Geolodthedwarf/PlanBook/planbook-cables/planbook-charger-cable.png

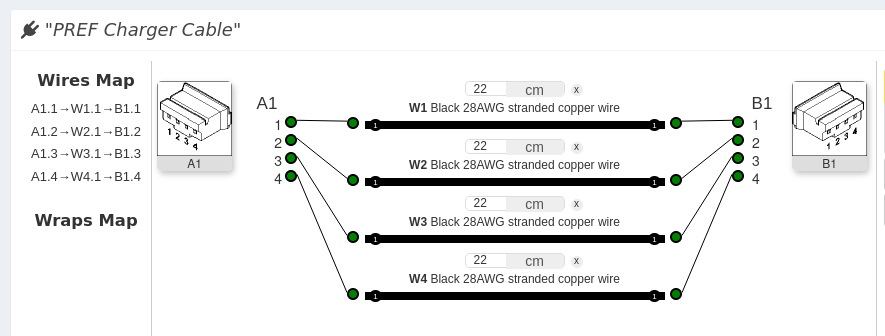
planbook-cables/planbook-charger-cable.png
