Geolodthedwarf/PlanBook/planbook-wifi/3d-models/User Library-PCIe_M_2_Key-E_2230_RF.STEP

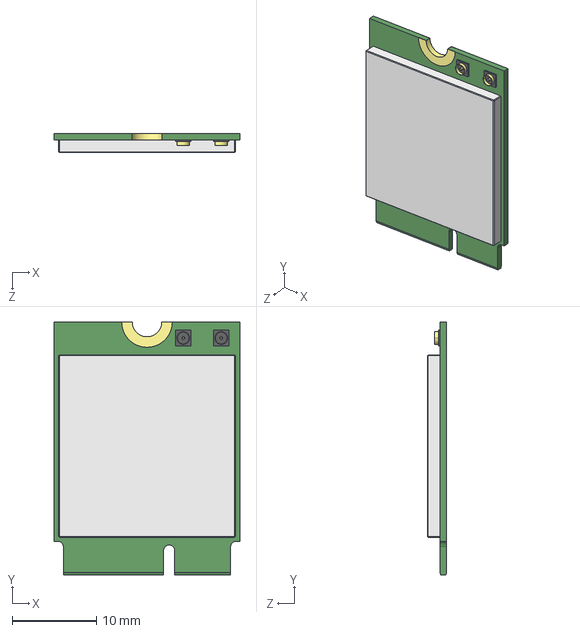
[picture p18: CAD file, 2026-09-27]
planbook-wifi/3d-models/User Library-PCIe_M_2_Key-E_2230_RF.STEP
22.0 x 30.0 x 2.30 mm
