Geolodthedwarf/PlanBook/planbook-3d-printed-parts/battery-holder-2025-11-18/PlanBook_Batt_Holder_18_11_25_V3_Mirrored.stl

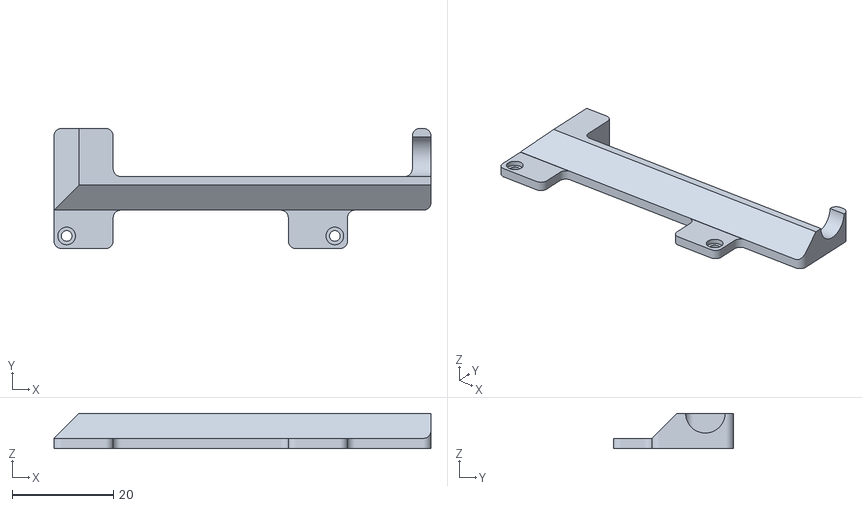
[picture p19: CAD file, 2026-09-27]
planbook-3d-printed-parts/battery-holder-2025-11-18/PlanBook_Batt_Holder_18_11_25_V3_Mirrored.stl
74.5 x 23.8 x 7.00
