Geolodthedwarf/PlanBook/planbook-case-20231121/PLANBOOK-bottom_enclosure_2023.09.06.step

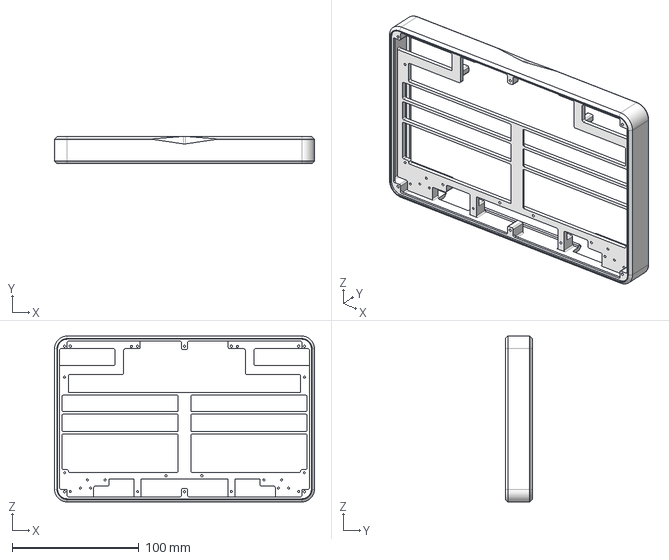
[picture p20: CAD file, 2026-09-27]
planbook-case-20231121/PLANBOOK-bottom_enclosure_2023.09.06.step
205.4 x 21.7 x 131.0 mm
