Geolodthedwarf/PlanBook/planbook-charger/3d-models/S2B-PH-SM4-TB.stp

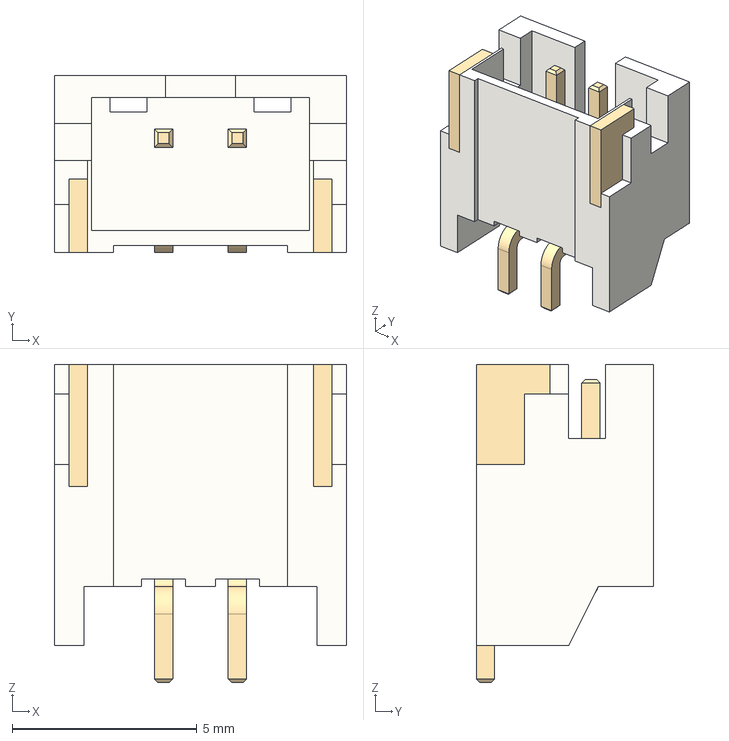
[picture p21: CAD file, 2026-09-27]
planbook-charger/3d-models/S2B-PH-SM4-TB.stp
7.90 x 4.80 x 8.60 mm
