Geolodthedwarf/PlanBook/planbook-headphones/3d-models/SR42W001.stp

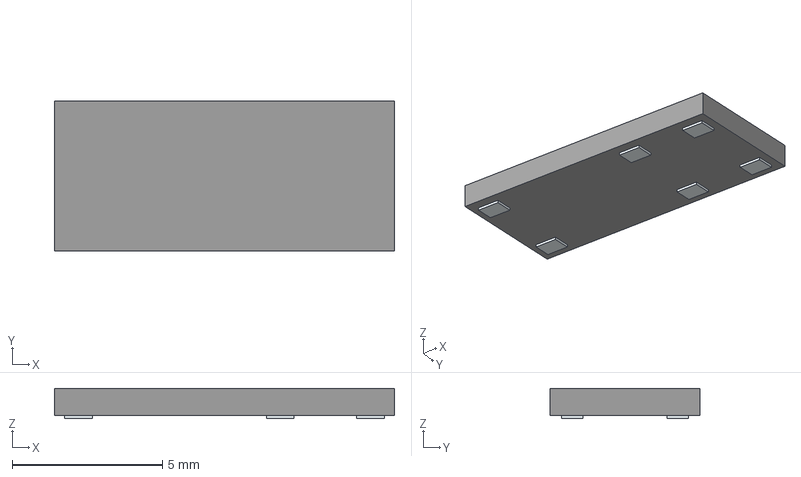
[picture p22: CAD file, 2026-09-27]
planbook-headphones/3d-models/SR42W001.stp
11.3 x 5.00 x 1.00 mm
Pins
