Geolodthedwarf/PlanBook/planbook-keyboard-kailh-ortho/3d-models/S4B-PH-SM4-TB.stp

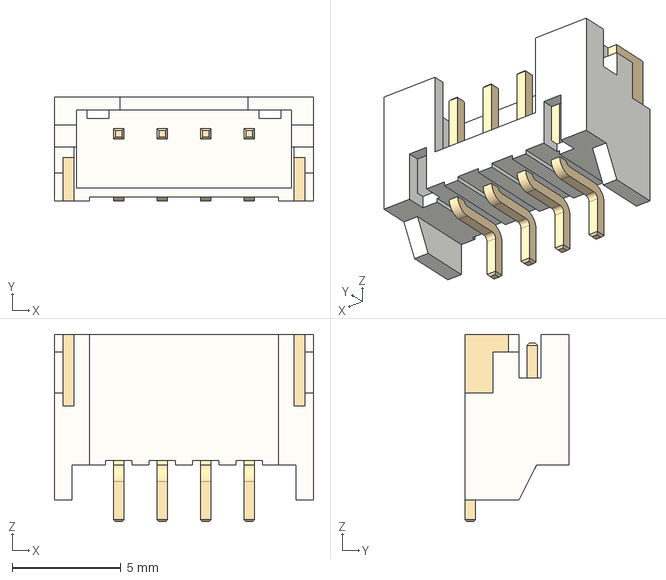
[picture p23: CAD file, 2026-09-27]
planbook-keyboard-kailh-ortho/3d-models/S4B-PH-SM4-TB.stp
11.9 x 4.80 x 8.60 mm
