Geolodthedwarf/PlanBook/planbook-wifi/3d-models/SM02B-SRSS-TB-LF--SN---3DModel-STEP-56544.STEP

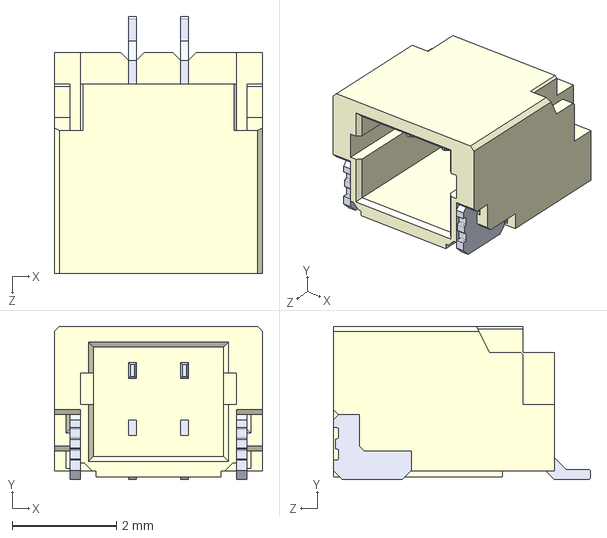
[picture p24: CAD file, 2026-09-27]
planbook-wifi/3d-models/SM02B-SRSS-TB-LF--SN---3DModel-STEP-56544.STEP
4.00 x 2.95 x 4.95 mm
