Geolodthedwarf/PlanBook/planbook-charger/3d-models/User Library-MWSA0518S.STEP

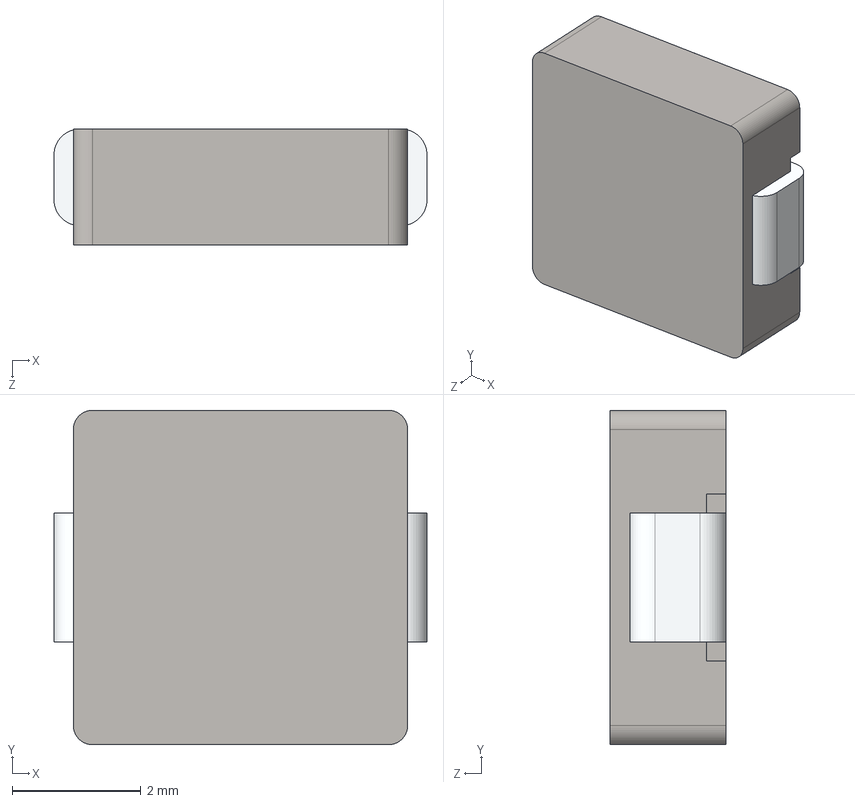
[picture p25: CAD file, 2026-09-27]
planbook-charger/3d-models/User Library-MWSA0518S.STEP
5.80 x 5.20 x 1.80 mm
MWSA0518S-HOUSE
MWSA0518S-PIN
