Geolodthedwarf/PlanBook/planbook-keyboard-kailh-ortho/3d-models/W25Q32JVSSIQ--3DModel-STEP-269445.STEP

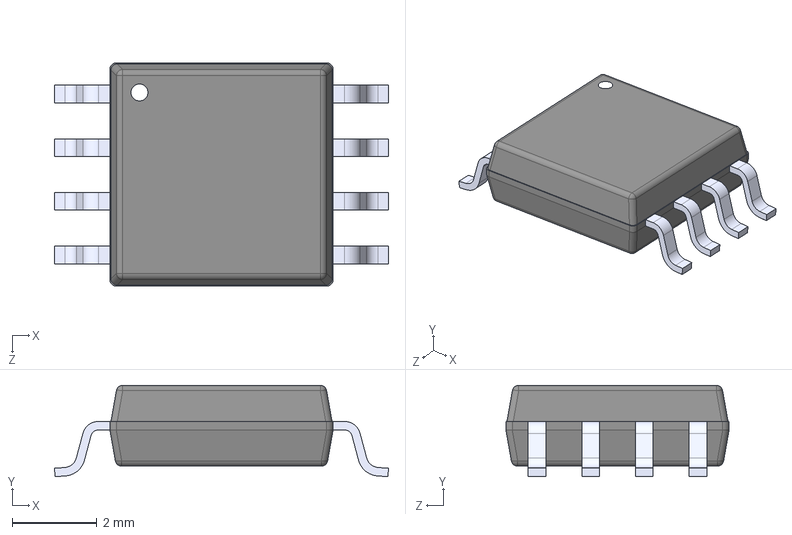
[picture p26: CAD file, 2026-09-27]
planbook-keyboard-kailh-ortho/3d-models/W25Q32JVSSIQ--3DModel-STEP-269445.STEP
7.90 x 2.16 x 5.28 mm
