Geolodthedwarf/PlanBook/planbook-motherboard/3d-models/SOD-128.step

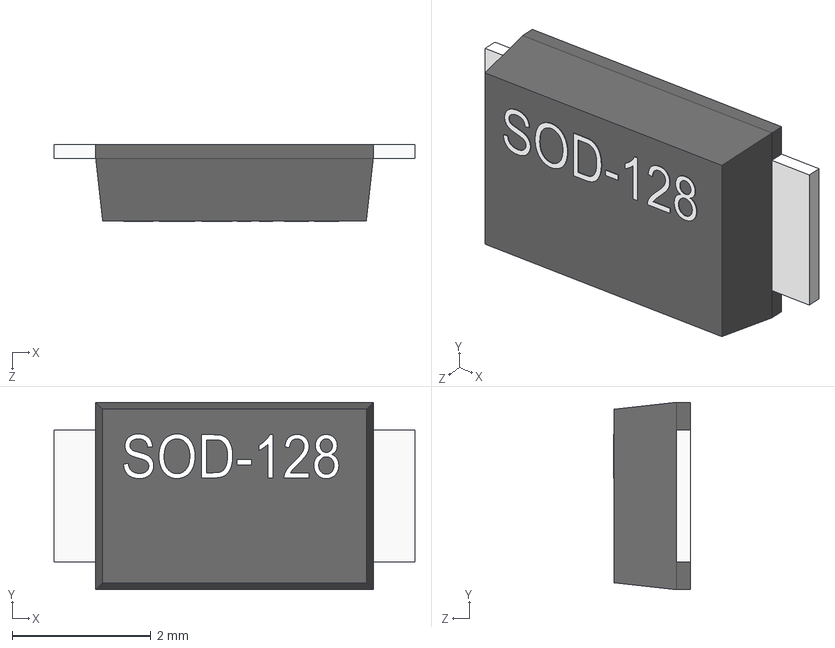
[picture p27: CAD file, 2026-09-27]
planbook-motherboard/3d-models/SOD-128.step
5.20 x 2.70 x 1.11 mm
