Geolodthedwarf/PlanBook/planbook-wifi/3d-models/CUI_SJ-43516-SMT-TR.step

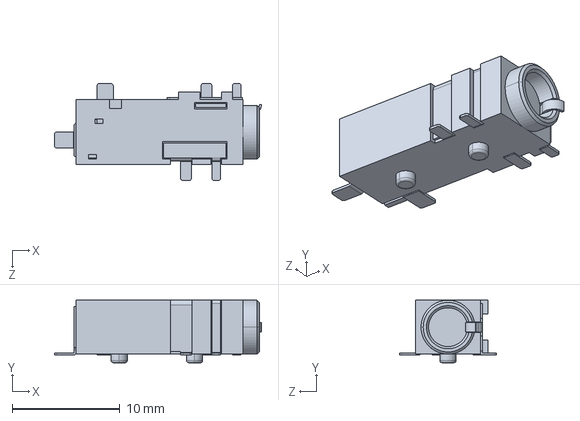
[picture p28: CAD file, 2026-09-27]
planbook-wifi/3d-models/CUI_SJ-43516-SMT-TR.step
19.2 x 5.80 x 9.00 mm
