Geolodthedwarf/PlanBook/planbook-charger/3d-models/S9B-PH-SM4-TB.stp

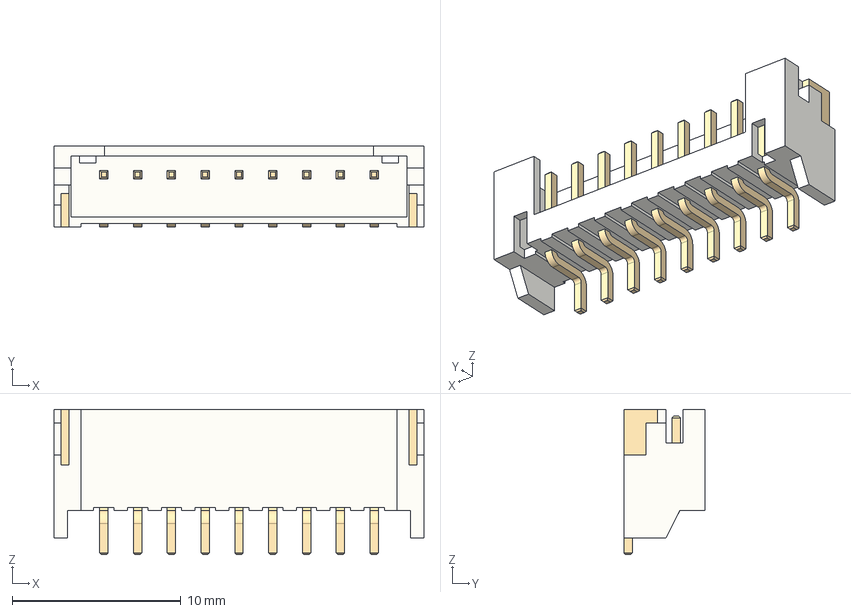
[picture p29: CAD file, 2026-09-27]
planbook-charger/3d-models/S9B-PH-SM4-TB.stp
21.9 x 4.80 x 8.60 mm
