Geolodthedwarf/PlanBook/planbook-headphones/3d-models/SM05B-SRSS-TB(LF)(SN)--3DModel-STEP-418109.STEP

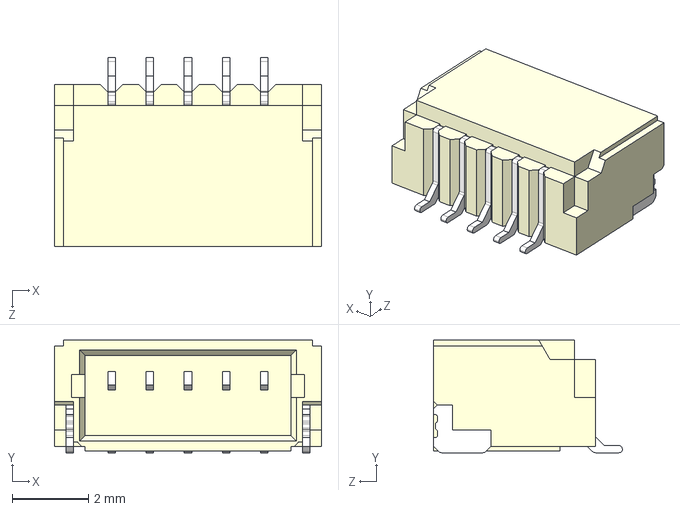
[picture p30: CAD file, 2026-09-27]
planbook-headphones/3d-models/SM05B-SRSS-TB(LF)(SN)--3DModel-STEP-418109.STEP
7.00 x 2.95 x 4.95 mm
