Geolodthedwarf/PlanBook/planbook-keyboard-kailh-ortho/3d-models/KMR221GLFS.step

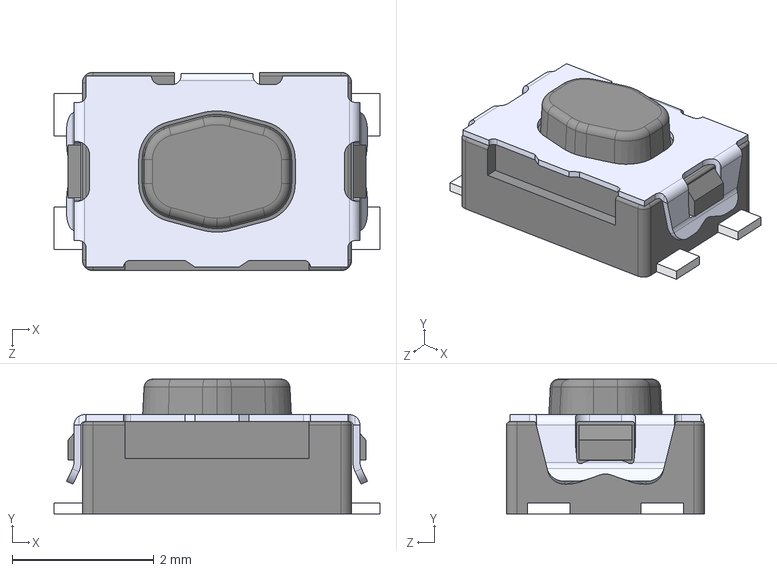
[picture p31: CAD file, 2026-09-27]
planbook-keyboard-kailh-ortho/3d-models/KMR221GLFS.step
4.60 x 1.90 x 2.80 mm
