Geolodthedwarf/PlanBook/planbook-motherboard/3d-models/SON95P300X300X80-7N.step

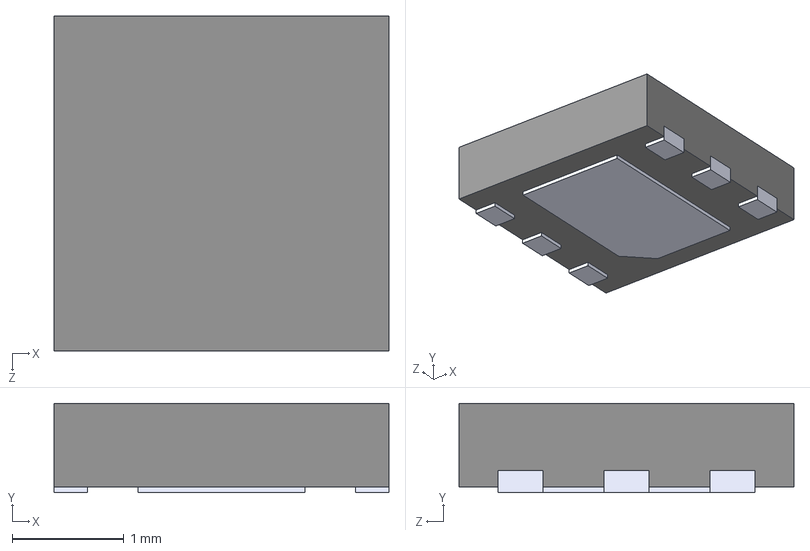
[picture p32: CAD file, 2026-09-27]
planbook-motherboard/3d-models/SON95P300X300X80-7N.step
3.00 x 0.8 x 3.00 mm
