Geolodthedwarf/PlanBook/planbook-motherboard/3d-models/CM2020-00TR--3DModel-STEP-56544.STEP

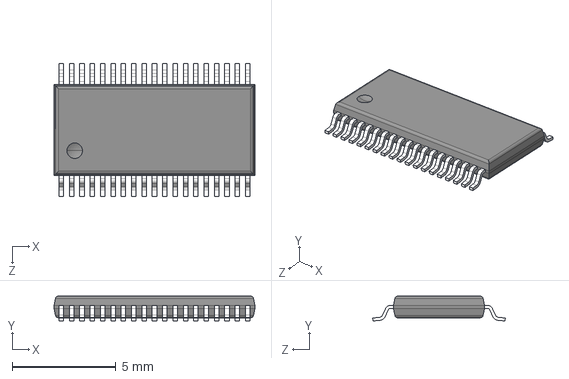
[picture p33: CAD file, 2026-09-27]
planbook-motherboard/3d-models/CM2020-00TR--3DModel-STEP-56544.STEP
9.70 x 1.20 x 6.40 mm
