Geolodthedwarf/PlanBook/planbook-motherboard/3d-models/User Library-VQFN-100 12X12 40P.STEP

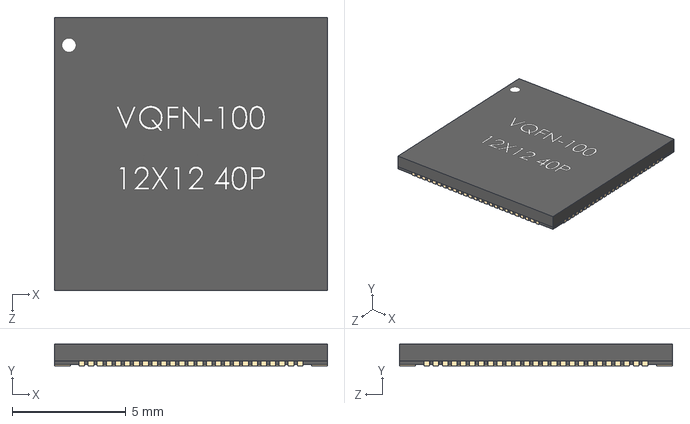
[picture p34: CAD file, 2026-09-27]
planbook-motherboard/3d-models/User Library-VQFN-100 12X12 40P.STEP
12.0 x 0.951 x 12.0 mm
