Geolodthedwarf/PlanBook/planbook-motherboard/3d-models/IND_TAIYO_NRH3012_TAY.step

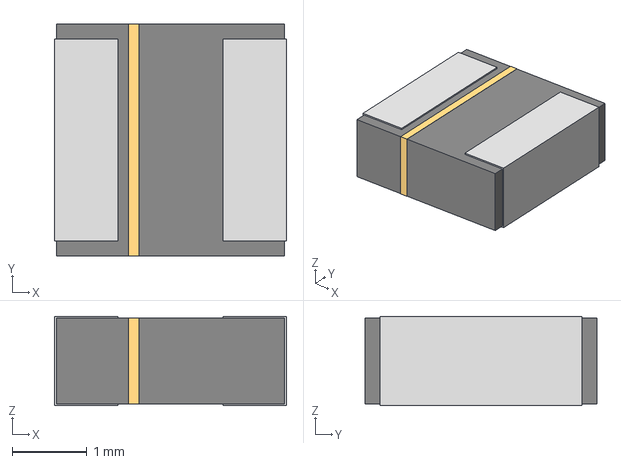
[picture p35: CAD file, 2026-09-27]
planbook-motherboard/3d-models/IND_TAIYO_NRH3012_TAY.step
3.10 x 3.10 x 1.19 mm
