Geolodthedwarf/PlanBook/planbook-wifi/3d-models/c-2199119-4-c-3d.stp

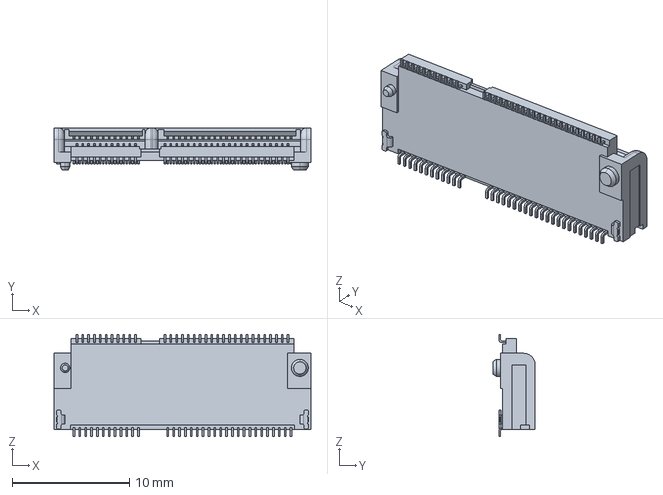
[picture p36: CAD file, 2026-09-27]
planbook-wifi/3d-models/c-2199119-4-c-3d.stp
21.9 x 3.62 x 8.70 mm
