Geolodthedwarf/PlanBook/planbook-motherboard/3d-models/HDMI-SMD_BX-HDMI-2-M19P.step

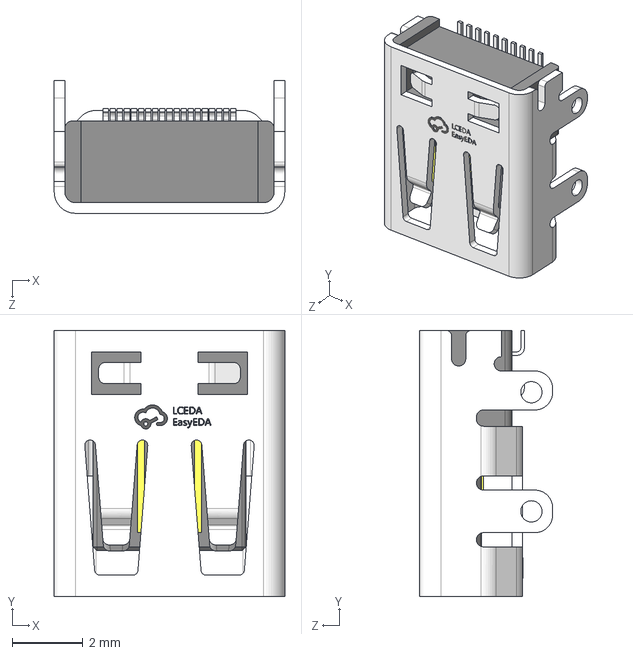
[picture p37: CAD file, 2026-09-27]
planbook-motherboard/3d-models/HDMI-SMD_BX-HDMI-2-M19P.step
6.50 x 7.50 x 3.76 mm
