Geolodthedwarf/PlanBook/planbook-motherboard/3d-models/DM3AT-SF-PEJM5--3DModel-STEP-56544.STEP

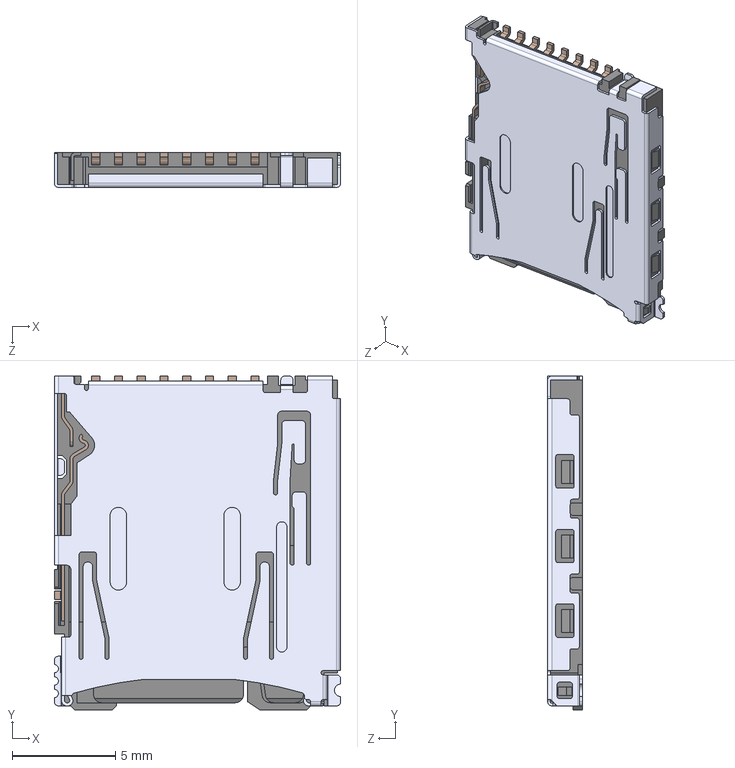
[picture p38: CAD file, 2026-09-27]
planbook-motherboard/3d-models/DM3AT-SF-PEJM5--3DModel-STEP-56544.STEP
13.8 x 16.2 x 1.68 mm
