Geolodthedwarf/PlanBook/planbook-motherboard/3d-models/c-1717254-1-d1-3d.stp

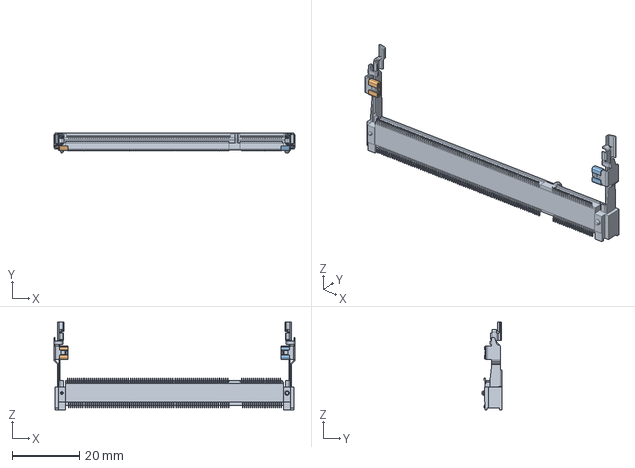
[picture p39: CAD file, 2026-09-27]
planbook-motherboard/3d-models/c-1717254-1-d1-3d.stp
71.5 x 5.90 x 26.0 mm
