Geolodthedwarf/PlanBook/planbook-motherboard/3d-models/ssfv33r_1stlf.stp

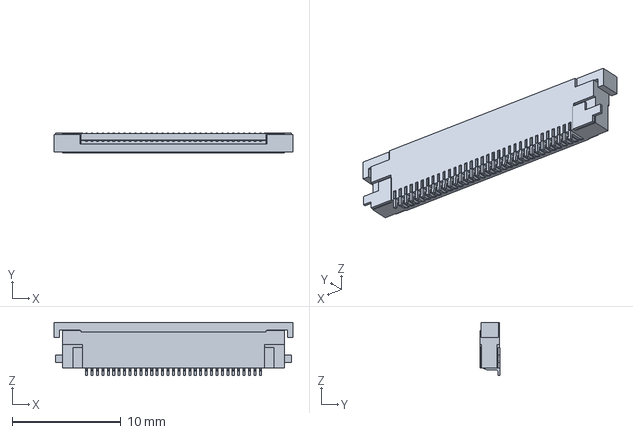
[picture p40: CAD file, 2026-09-27]
planbook-motherboard/3d-models/ssfv33r_1stlf.stp
22.0 x 1.87 x 4.90 mm
