Geolodthedwarf/PlanBook/planbook-motherboard/3d-models/BK-879.STEP

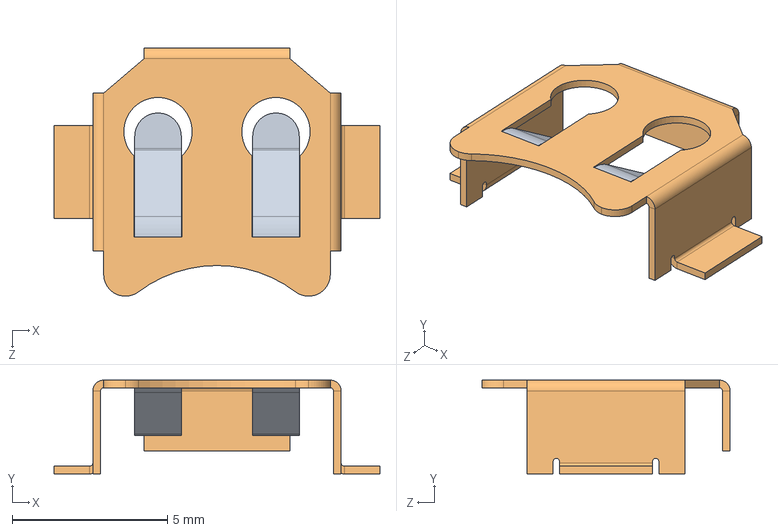
[picture p41: CAD file, 2026-09-27]
planbook-motherboard/3d-models/BK-879.STEP
10.5 x 3.02 x 8.00 mm
