Geolodthedwarf/PlanBook/planbook-motherboard/3d-models/FUSB302BMPX.STEP

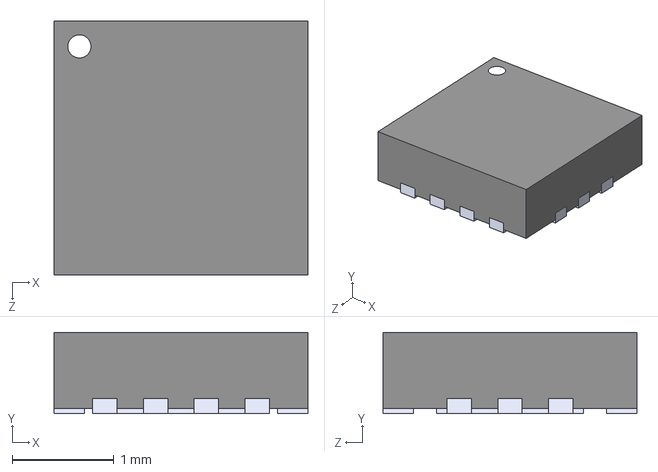
[picture p43: CAD file, 2026-09-27]
planbook-motherboard/3d-models/FUSB302BMPX.STEP
2.50 x 0.8 x 2.50 mm
