Geolodthedwarf/PlanBook/planbook-motherboard/3d-models/DM3CS-SF.stp

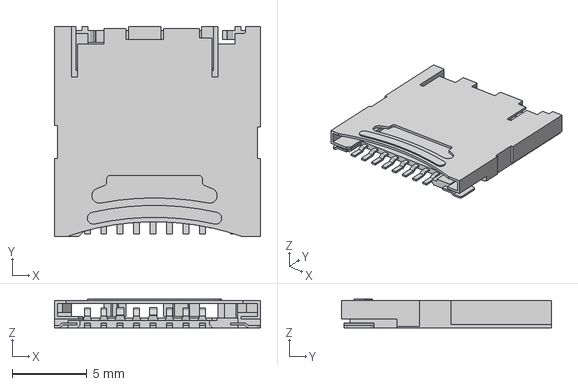
[picture p44: CAD file, 2026-09-27]
planbook-motherboard/3d-models/DM3CS-SF.stp
13.8 x 14.1 x 1.93 mm
