Geolodthedwarf/PlanBook/planbook-motherboard/3d-models/p36-2.stp

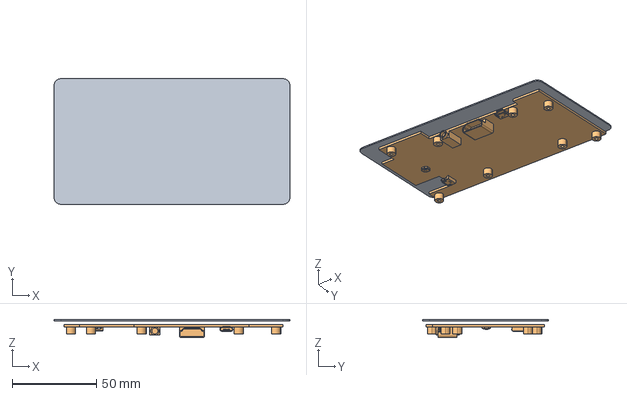
[picture p46: CAD file, 2026-09-27]
planbook-motherboard/3d-models/p36-2.stp
140.4 x 74.8 x 10.8 mm
