Geolodthedwarf/PlanBook/planbook-motherboard/3d-models/TSM-106-02-X-SH-A.step

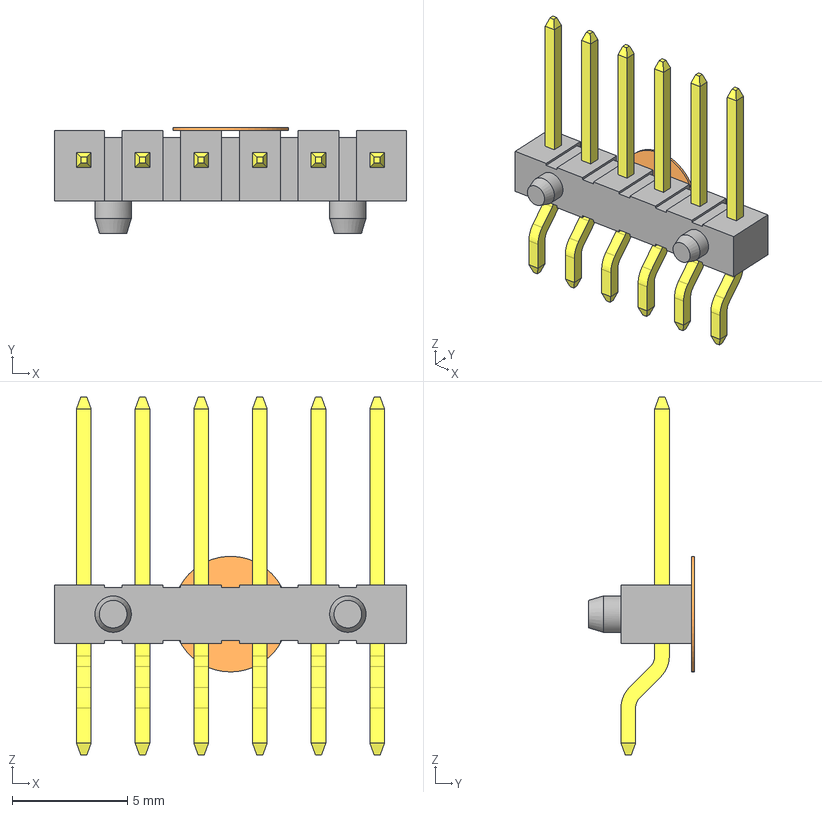
[picture p47: CAD file, 2026-09-27]
planbook-motherboard/3d-models/TSM-106-02-X-SH-A.step
15.2 x 4.57 x 15.5 mm
T-1S6-15(-02-6-SH)
TSM_polyimide_film
TSM-106-02-SH-A_body
