Geolodthedwarf/PlanBook/planbook-motherboard/3d-models/TLV320AIC3100IRHBR.STEP

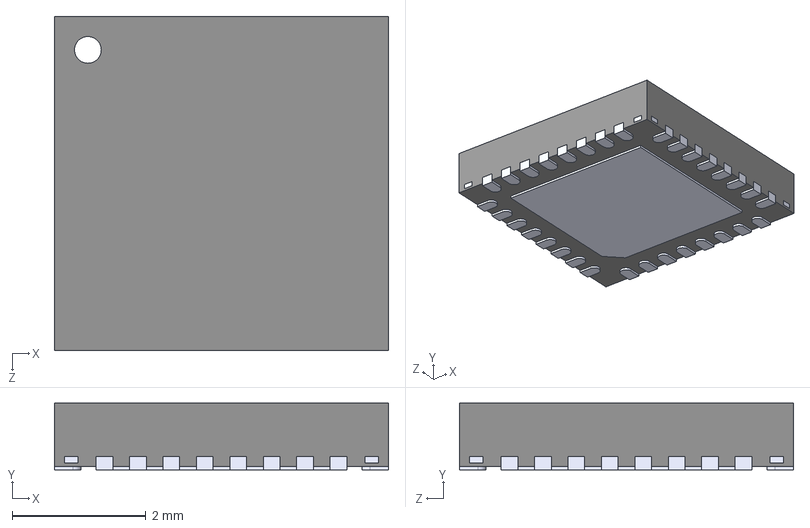
[picture p48: CAD file, 2026-09-27]
planbook-motherboard/3d-models/TLV320AIC3100IRHBR.STEP
5.00 x 1.00 x 5.00 mm
