Geolodthedwarf/PlanBook/planbook-motherboard/3d-models/IHLP4040DZ (2.2-100uH).STEP

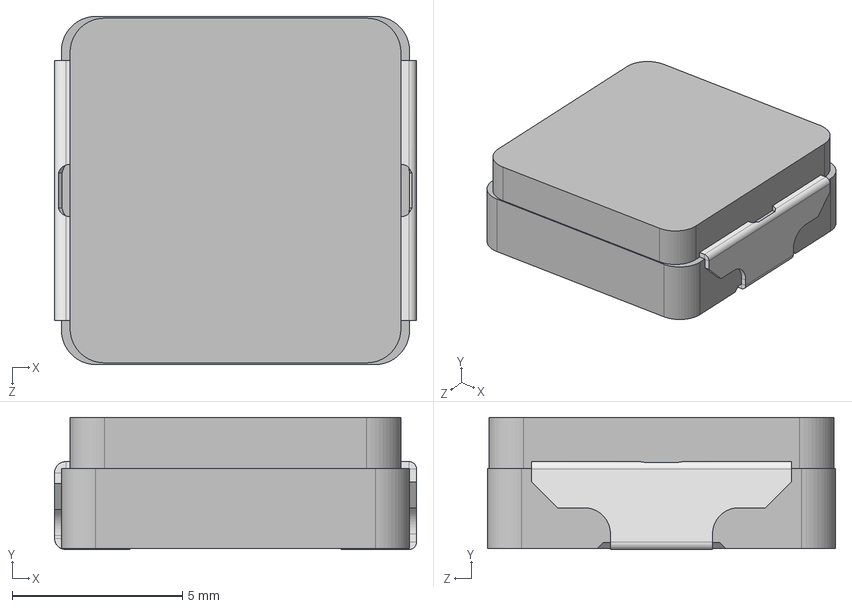
[picture p49: CAD file, 2026-09-27]
planbook-motherboard/3d-models/IHLP4040DZ (2.2-100uH).STEP
10.6 x 3.87 x 10.2 mm
