Geolodthedwarf/PlanBook/planbook-motherboard/3d-models/MP23ABS1TR.obj

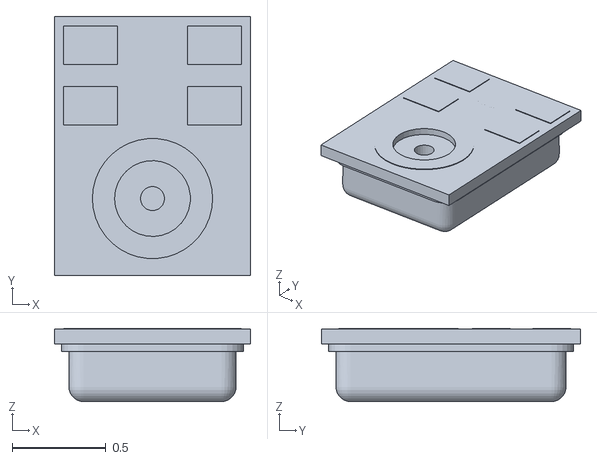
[picture p50: CAD file, 2026-09-27]
planbook-motherboard/3d-models/MP23ABS1TR.obj
1.04 x 1.38 x 0.39
