Geolodthedwarf/PlanBook/planbook-motherboard/3d-models/19-337-R6GHBHC-A01-2T.STEP

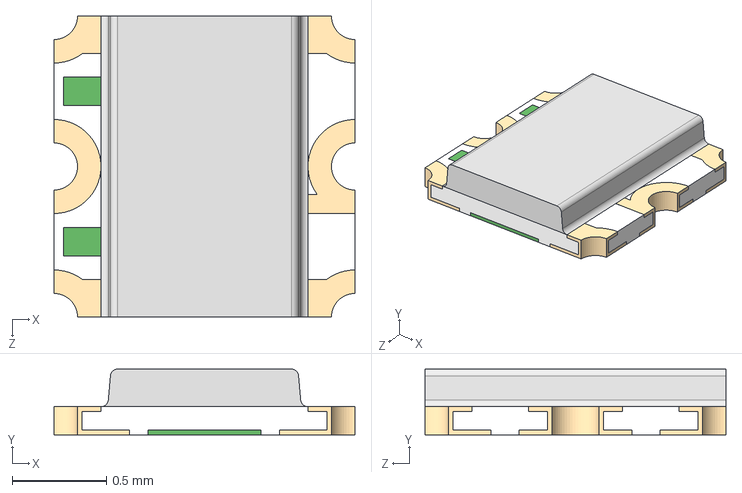
[picture p51: CAD file, 2026-09-27]
planbook-motherboard/3d-models/19-337-R6GHBHC-A01-2T.STEP
1.60 x 0.35 x 1.60 mm
