Geolodthedwarf/PlanBook/planbook-motherboard/3d-models/TYPE-C-31-M-12--3DModel-STEP-56544.STEP

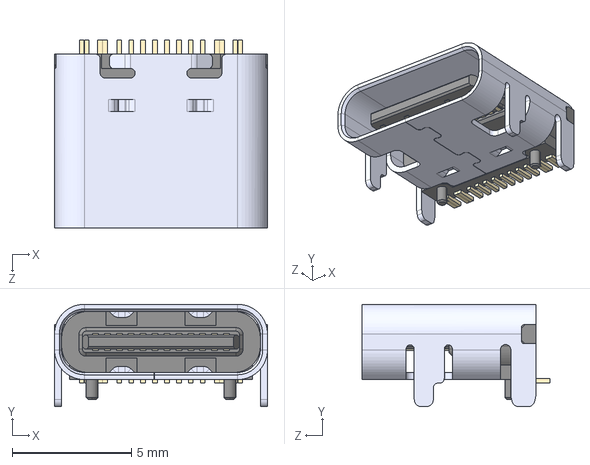
[picture p52: CAD file, 2026-09-27]
planbook-motherboard/3d-models/TYPE-C-31-M-12--3DModel-STEP-56544.STEP
8.94 x 4.30 x 7.90 mm
