Geolodthedwarf/PlanBook/planbook-motherboard/3d-models/Bateria 18650 3.7 V 1300 mAh d.18 mm.STEP

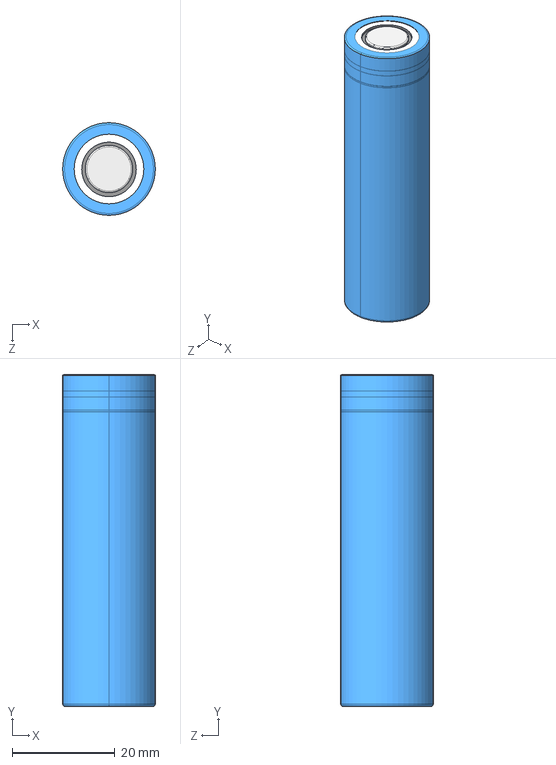
[picture p53: CAD file, 2026-09-27]
planbook-motherboard/3d-models/Bateria 18650 3.7 V 1300 mAh d.18 mm.STEP
18.1 x 64.7 x 18.1 mm
