Geolodthedwarf/PlanBook/planbook-motherboard/3d-models/keystone-PN54.STEP

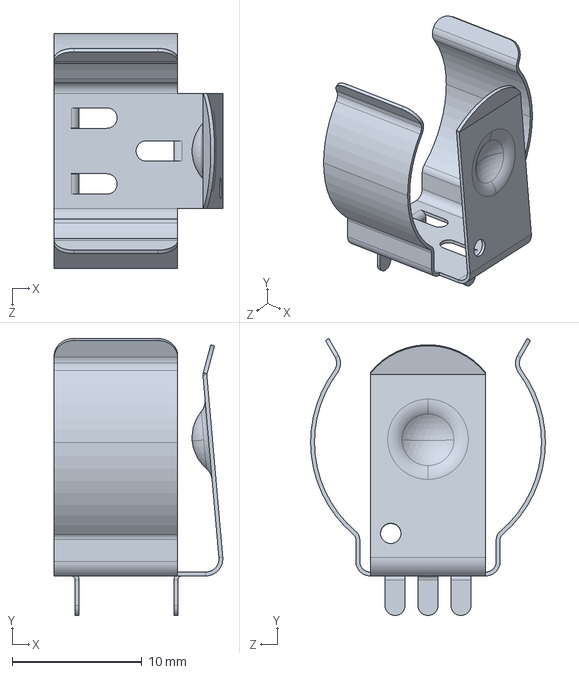
[picture p54: CAD file, 2026-09-27]
planbook-motherboard/3d-models/keystone-PN54.STEP
13.0 x 21.4 x 18.1 mm
