Geolodthedwarf/PlanBook/planbook-motherboard/3d-models/STP_NIT8M_SOM_REV10_20190228.step

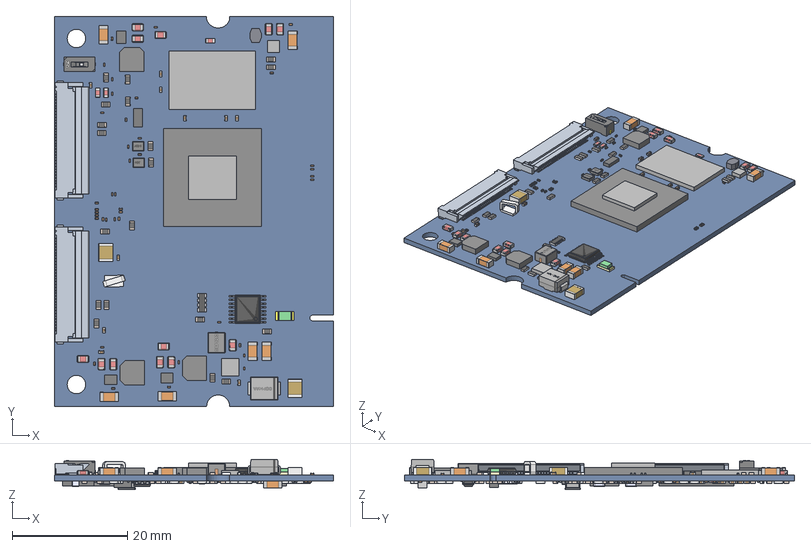
[picture p55: CAD file, 2026-09-27]
planbook-motherboard/3d-models/STP_NIT8M_SOM_REV10_20190228.step
48.4 x 67.6 x 5.23 mm
Board
CAP0201_(0603) x 175
cay16-j4 x 2
Extruded x 16
CAP0402 x 43
CAPC3225X13 x 2
Chip_Cap_MLCC_1206_(3216)_D x 7
SW3dPS-LED1206G_Extruded
SW3dPS-LED1206G_Extruded4
SW3dPS-LED1206G_Extruded2 x 2
SW3dPS-LED1206G_Extruded1
SW3dPS-LED1206G_Extruded3
SW3dPS-LED1206G_Board
DO-214AA(SMB)
XF2M_3315_1A x 2
_CHS-01-J-body
_CHS-slider
ABM11_RGB4210752 x 3
User_Library-GP
