Geolodthedwarf/PlanBook/planbook-motherboard/3d-models/JXD-G2406S.obj

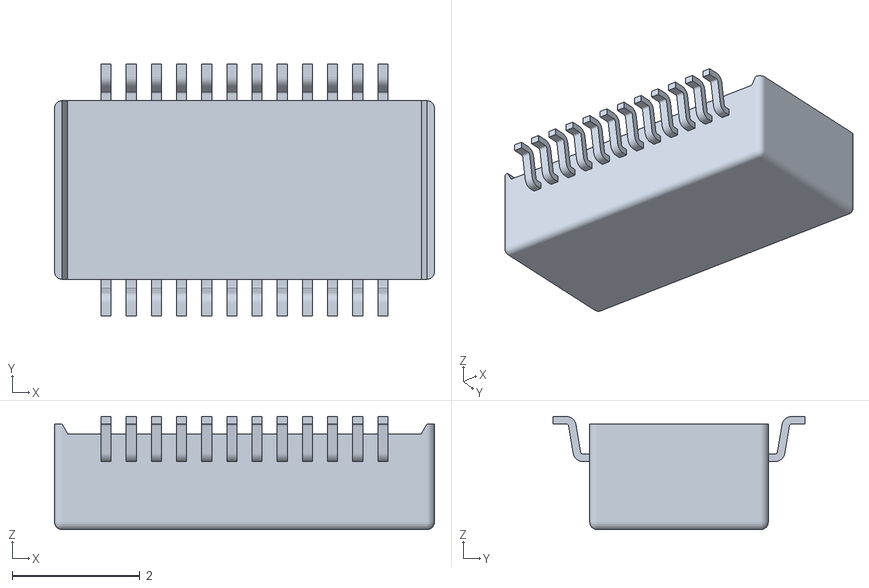
[picture p56: CAD file, 2026-09-27]
planbook-motherboard/3d-models/JXD-G2406S.obj
5.94 x 3.94 x 1.77
