Geolodthedwarf/PlanBook/planbook-motherboard/3d-models/c-2199337-5-a-3d.stp

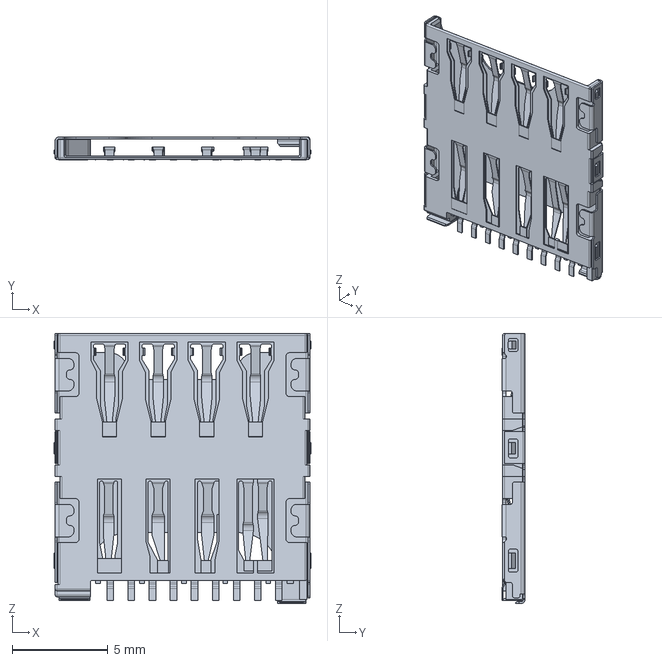
[picture p57: CAD file, 2026-09-27]
planbook-motherboard/3d-models/c-2199337-5-a-3d.stp
13.4 x 1.20 x 14.1 mm
