Geolodthedwarf/PlanBook/planbook-motherboard/3d-models/Amphenol_-_12401548E4#2A.step

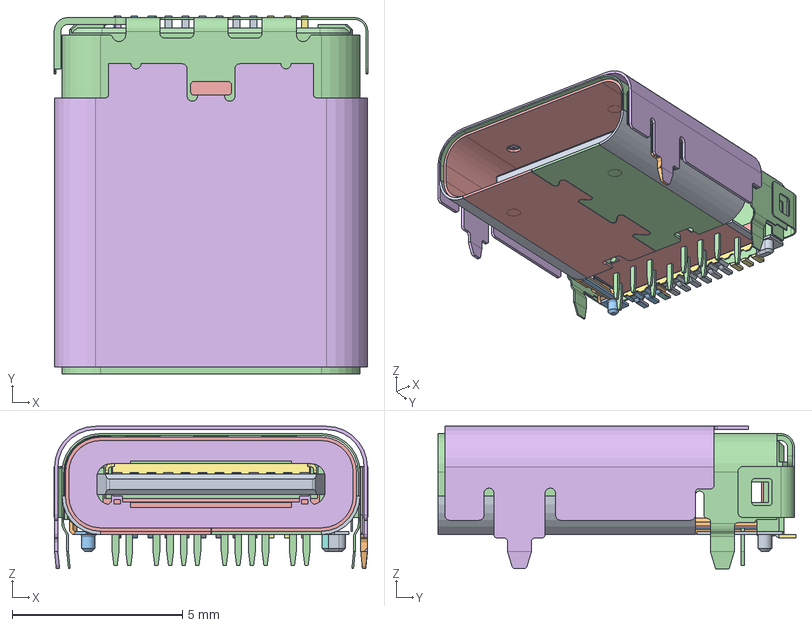
[picture p58: CAD file, 2026-09-27]
planbook-motherboard/3d-models/Amphenol_-_12401548E4#2A.step
9.20 x 10.5 x 4.18 mm
