Geolodthedwarf/PlanBook/planbook-motherboard/3d-models/C-1-2199230-5-blk.step

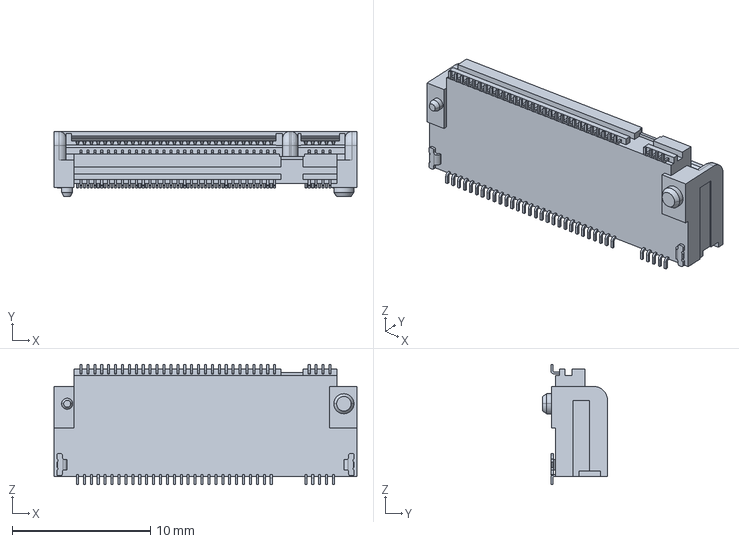
[picture p59: CAD file, 2026-09-27]
planbook-motherboard/3d-models/C-1-2199230-5-blk.step
21.9 x 4.70 x 8.70 mm
