Geolodthedwarf/PlanBook/planbook-motherboard/3d-models/FH12-33S-0.5SH.stp

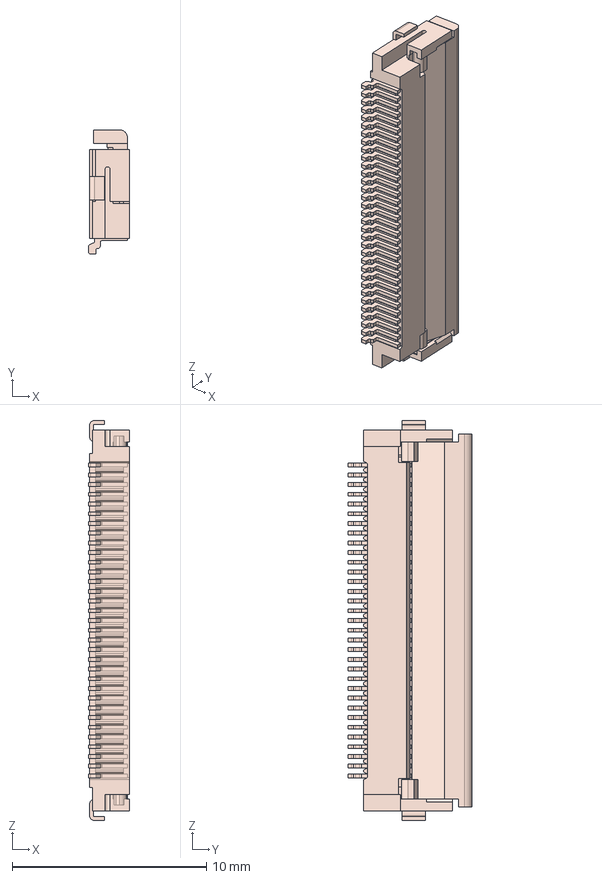
[picture p60: CAD file, 2026-09-27]
planbook-motherboard/3d-models/FH12-33S-0.5SH.stp
2.10 x 6.40 x 20.6 mm
