Geolodthedwarf/PlanBook/planbook-motherboard/3d-models/3215-crystal.step

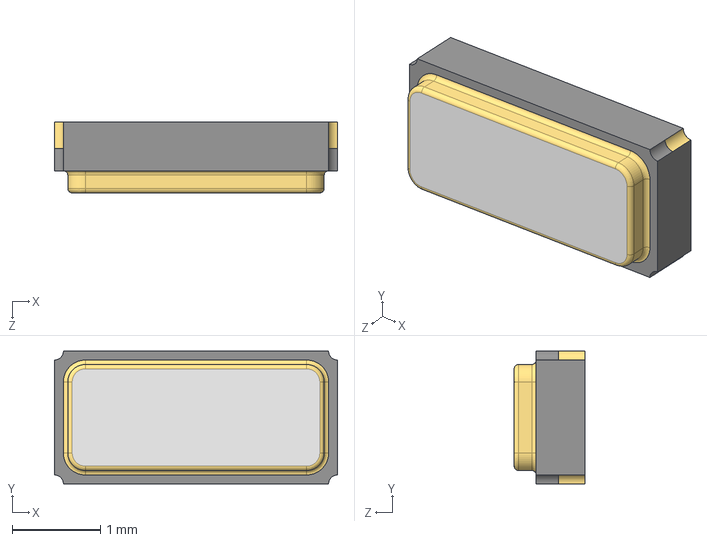
[picture p61: CAD file, 2026-09-27]
planbook-motherboard/3d-models/3215-crystal.step
3.20 x 1.50 x 0.8 mm
