Geolodthedwarf/PlanBook/planbook-motherboard/3d-models/HTQFP-80.stp

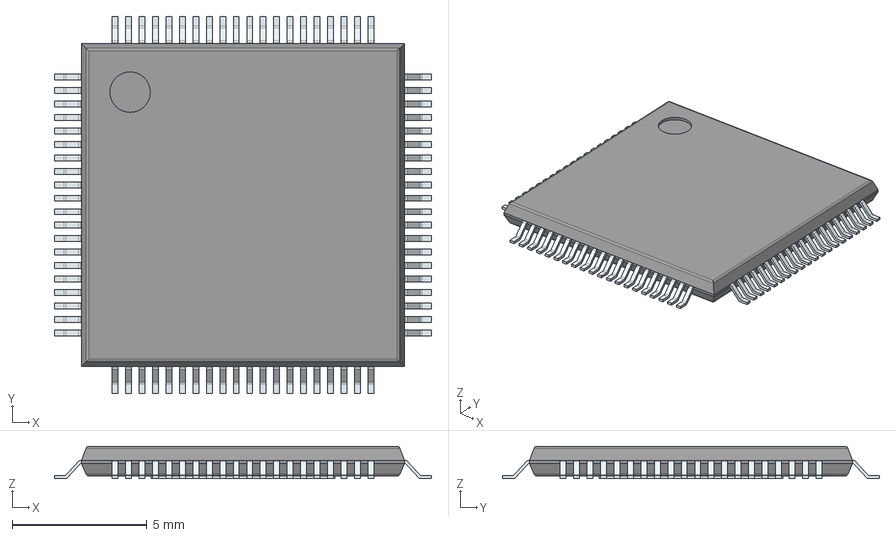
[picture p62: CAD file, 2026-09-27]
planbook-motherboard/3d-models/HTQFP-80.stp
14.0 x 14.0 x 1.20 mm
PinsArrayLR
PinsArrayTB
ThermalPad
