Geolodthedwarf/PlanBook/planbook-motherboard/3d-models/RET0040A.stp

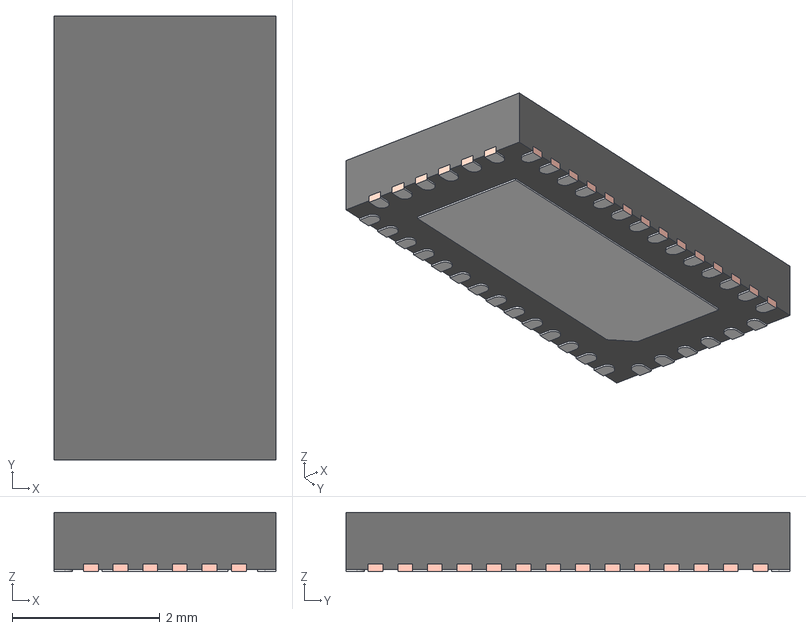
[picture p63: CAD file, 2026-09-27]
planbook-motherboard/3d-models/RET0040A.stp
3.00 x 6.00 x 0.8 mm
RET0040A_FRAME
RET0040A_BODY
RET0040A_PIN1_AREA
