Geolodthedwarf/PlanBook/planbook-keyboard-fw/planbook-hid/src/menu.h

/*
  SPDX-License-Identifier: GPL-3.0-or-later
  PlanBook Keyboard/Trackball Controller Firmware for RP2040
  Copyright 2021-2024 PlanBook Project
*/

#ifndef _MENU_H_
#define _MENU_H_

#include <stdint.h>

struct menu_item {
  const char* title;
  int keycode;
};

#define MENU_PAGE_NONE 0
#define MENU_PAGE_OTHER 1
#define MENU_PAGE_BATTERY_STATUS 2
#define MENU_PAGE_PLANBOOK_LOGO 3
#define MENU_PAGE_CONSOLE 4

void reset_and_render_menu(void);
void reset_menu(void);
void render_menu(int y);
void refresh_menu_page(void);
int execute_menu_row_function(int y);
int input_menu_key(uint8_t keycode, uint8_t shift);
void render_tina(void);
void anim_hello(void);
void anim_goodbye(void);

#endif
